Sergio1092/ProyectoCapstone-TotalLifeProtect/Fotografías del Proyecto/Detector CO-CO2-GLP (1).jpeg

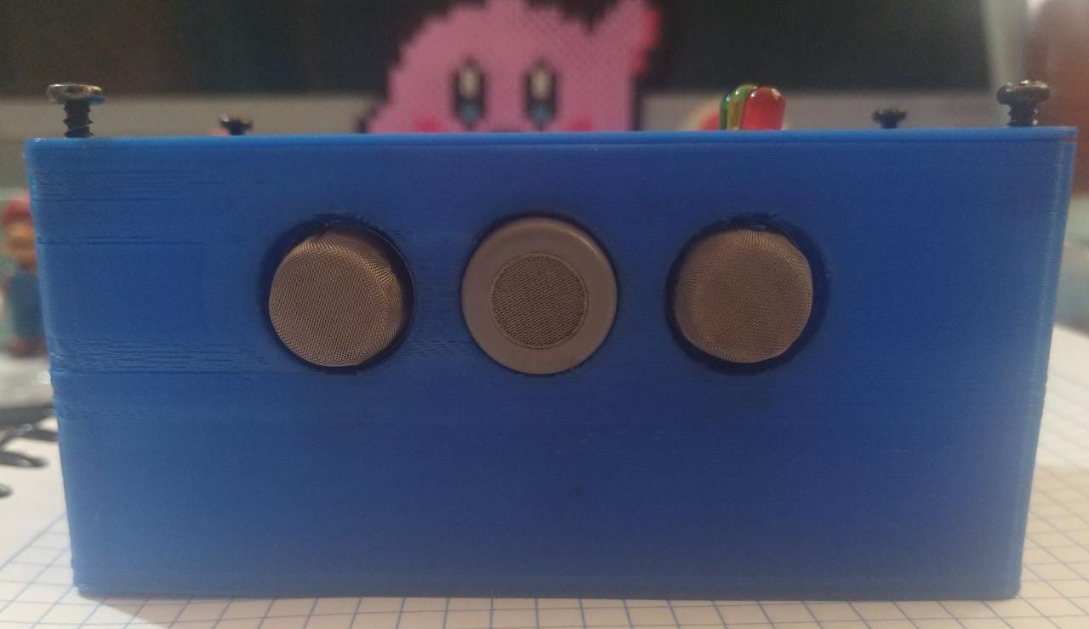
Fotografías del Proyecto/Detector CO-CO2-GLP (1).jpeg
